AC807/CO2-Led-Matrix-/Pres und bilder/IMG_20220207_161630.jpg

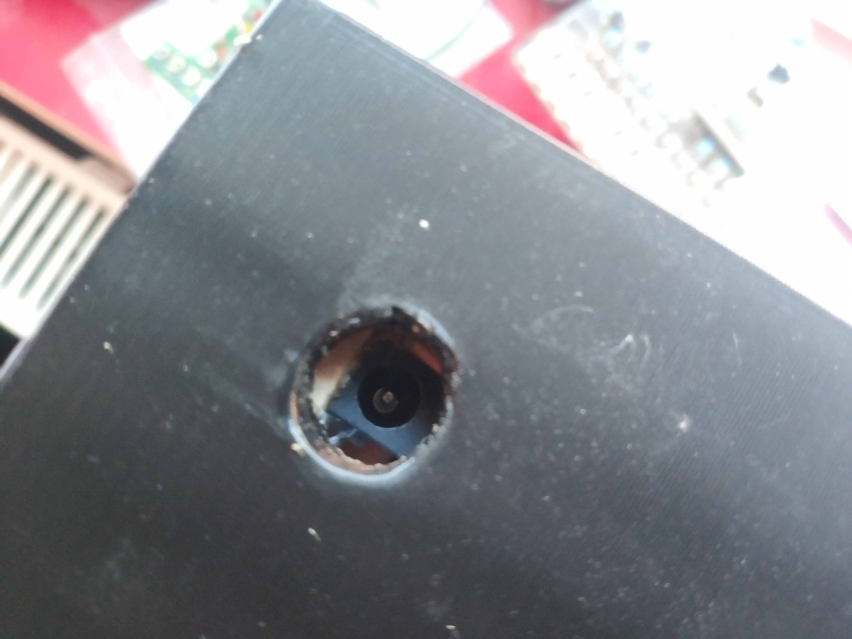
Pres und bilder/IMG_20220207_161630.jpg
