AC807/CO2-Led-Matrix-/Pres und bilder/Photos-001 (1)/IMG_20211016_115225.jpg

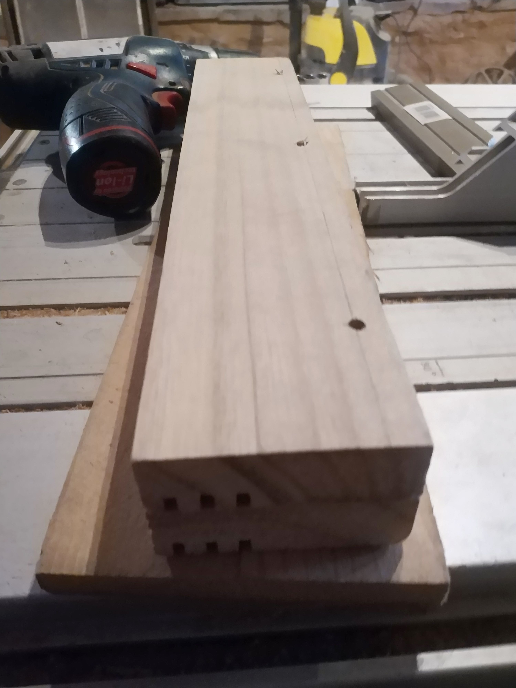
Pres und bilder/Photos-001 (1)/IMG_20211016_115225.jpg
